ARTS-Laboratory/LPBF-Observer/system_development/Damascus/V0.5.0/software development/Event Camera/v0.2/README.md

# Python Virtual Environment Setup

## Overview

It is recommended to run the Event Camera software inside a Python virtual environment. This keeps the project's Python packages isolated from other Python installations and helps ensure that the required dependency versions are used.

> **Important:** Install the **Arena SDK** and **Arena Python API** as described below before running the Event Camera software.

------------------------------------------------------------------------

## Create a Virtual Environment

Open Command Prompt or PowerShell and navigate to the Event Camera project directory.

Create a Python virtual environment named `megaforehead`:

```bash
python -m venv megaforehead
```

Activate the virtual environment.

### Windows

```bash
megaforehead\Scripts\activate
```

### Linux

```bash
source megaforehead/bin/activate
```

Once activated, the terminal should show `(.venv)` before the command prompt.

------------------------------------------------------------------------

## Install the Project Requirements

With the virtual environment activated, install the Python packages listed in `requirements.txt`:

```bash
python -m pip install -r requirements.txt
```

> **Note:** The `arena_api` package is supplied with the LUCID Arena SDK. If installation from `requirements.txt` cannot locate `arena_api`, install the Arena Python wheel from the Arena SDK as described in the **Arena Python API Installation** section below.

------------------------------------------------------------------------

# Arena SDK Installation Guide

## Overview

The camera software requires the **LUCID Arena SDK** to be installed before the camera can be detected and used.

> **Important:** During installation, you **must** enable **Developer Mode**. Failing to do so will result in missing development components required by the application.

------------------------------------------------------------------------

## Download the Arena SDK

Download the Arena SDK installer using the link below (You must make an account with Lucid):

**Arena SDK Installer:**

[Arena SDK Installer](https://thinklucid.com/downloads-hub/)

------------------------------------------------------------------------

## Installation Instructions

1. Download the Arena SDK installer from the link above.
2. Run the installer with administrator privileges.
3. Follow the installation wizard.
4. When prompted to select installation options, **enable Developer Mode**.

------------------------------------------------------------------------

## ⚠️ Critical Requirement: Enable Developer Mode

> **Developer Mode must be selected during installation.**

If Developer Mode is **not** selected:

- Required development libraries and headers will not be installed.
- The application may fail to detect or communicate with the camera.
- Camera SDK components required by the application will be missing.
- You may encounter runtime errors or application startup failures.
- The SDK may need to be completely reinstalled to add the missing components.

**Verify that the "Developer Mode" option is checked before proceeding with the installation.**

------------------------------------------------------------------------

## Developer Mode Installation

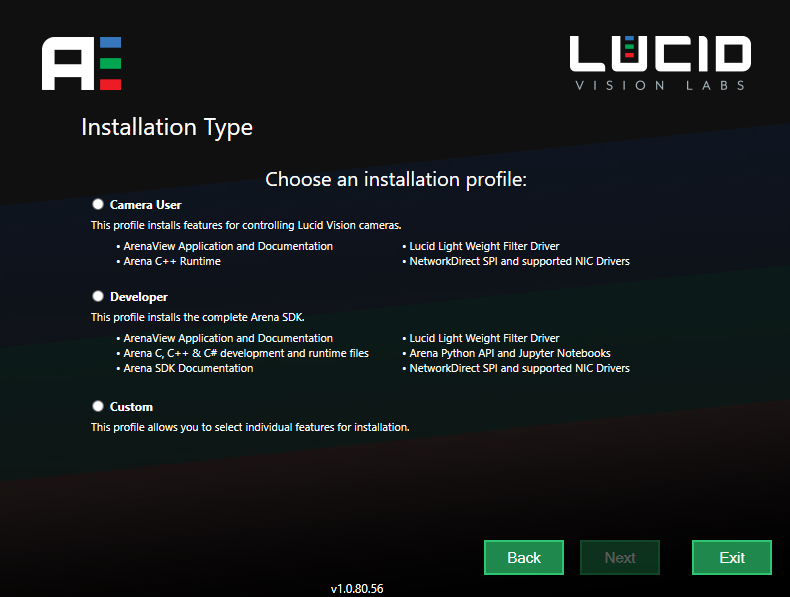
[picture p3: system_development/Damascus/V0.5.0/software development/Event Camera/v0.2/Media/DeveloperModeInstaller.png]


------------------------------------------------------------------------

## Verify the Installation

After installation:

- Launch **ArenaView**.
- Verify that your camera is detected.
- Confirm that you can start image acquisition successfully.
- If the camera is not detected, verify that Developer Mode was enabled during installation.

------------------------------------------------------------------------

## Troubleshooting

If the application cannot communicate with the camera:

1. Confirm that the Arena SDK is installed.
2. Verify that **Developer Mode** was selected during installation.
3. Restart the computer if prompted by the installer.
4. If Developer Mode was not selected, rerun the installer and modify or reinstall the SDK with Developer Mode enabled.

------------------------------------------------------------------------

## Additional Notes

Always install the version of the Arena SDK that matches the version required by this application. Using a different SDK version may result in compatibility issues.

# Network Adapter Configuration

## Overview

To help improve camera streaming performance and reduce dropped packets
or acquisition interruptions, configure your network adapter with the
highest supported values for the settings below.

> **Note:** Do **not** manually enter the values shown in example
> screenshots. Instead, configure each setting to the **maximum value
> allowed by your network adapter**.

## Configuration Steps

1.  Open **Network Connections**.
2.  Right-click the Ethernet adapter connected to the camera and select
    **Properties**.
3.  Click **Configure**.
4.  Open the **Advanced** tab.
5.  Locate the following settings:
    -   **Jumbo Packet**
    -   **Receive Buffer**
6.  Set each option to the **maximum value available** in the adapter's
    configuration.
7.  Click **OK** to save the changes.

------------------------------------------------------------------------

## Jumbo Packet

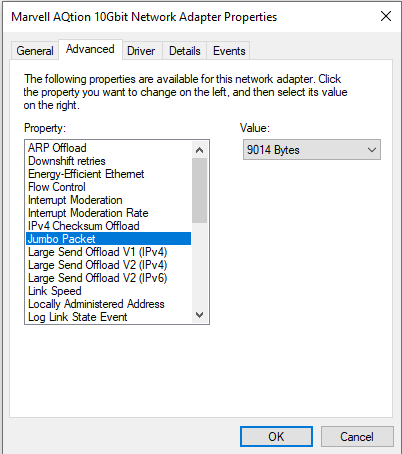
[picture p4: system_development/Damascus/V0.5.0/software development/Event Camera/v0.2/Media/JumboPacket.png]


------------------------------------------------------------------------

## Receive Buffer

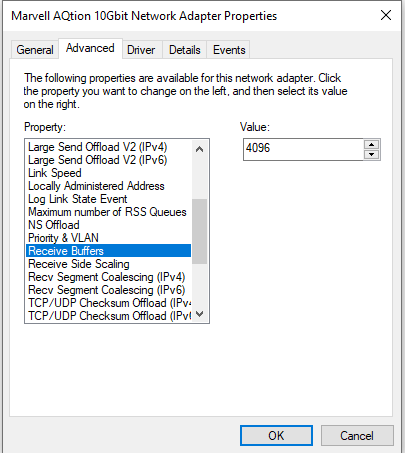
[picture p5: system_development/Damascus/V0.5.0/software development/Event Camera/v0.2/Media/ReceiveBuffers.png]


------------------------------------------------------------------------

## Notes

-   The maximum available values may differ depending on the network
    adapter manufacturer and model.
-   After changing these settings, restart the network connection or
    reboot the computer if required.
-   These settings are commonly used to improve the reliability of
    high-bandwidth GigE Vision camera streaming.

------------------------------------------------------------------------

## Verify the Device Link Speed

After configuring the network adapter, verify that the camera is operating at the expected network link speed.

### Why This Matters

If the **Device Link Speed** is lower than the camera's rated speed, the camera may experience:

- Reduced bandwidth
- Dropped packets
- Incomplete images
- Acquisition interruptions
- Reduced overall performance

### Expected Device Link Speed

The **Device Link Speed** reported in ArenaView should match the maximum speed supported by your camera.

| Camera Link Speed | Expected DeviceLinkSpeed |
|---|---:|
| 1 Gigabit (1G) | 1,000,000,000 bps |
| 2.5 Gigabit (2.5G)| 2,500,000,000 bps |
| 5 Gigabit (5G) | 5,000,000,000 bps |
| 10 Gigabit (10G)  | 10,000,000,000 bps |

### How to Check

1. Open **ArenaView**.
2. Connect to your camera.
3. Ensure the features toggle is set to "Complete" 
4. Open the **Features** panel.
5. Search for **Device Link Speed**.
6. Verify that the reported value matches your camera's expected link speed.

If the reported speed is lower than expected:

- Verify that the Ethernet adapter supports the camera's link speed.
- Confirm that the correct Ethernet port is being used.
- Check the network cable (Cat6/Cat6a recommended for higher-speed cameras).
- Ensure the network adapter drivers are up to date.
- Reboot the system after making any network configuration changes.

------------------------------------------------------------------------

## Change Packet Size Setting

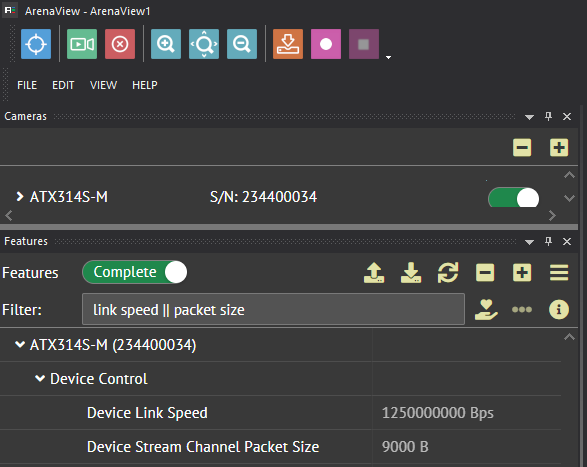
[picture p6: system_development/Damascus/V0.5.0/software development/Event Camera/v0.2/Media/9000B-Device-Stream-Channel-Packet-Size.png]


------------------------------------------------------------------------

# Arena Python API Installation

## Overview

The **Arena Python API** is a Python wrapper for the Arena SDK that allows Python applications to communicate with LUCID Vision cameras.

The Python API is built on top of the **Arena C API** and requires that the **Arena SDK** has already been installed.

> **Important:** Install the Arena SDK **before** installing the Arena Python API.

------------------------------------------------------------------------

## Prerequisites

Before installing the Arena Python API, ensure the following requirements are met:

- Python **3.6.8** or newer
- Arena SDK installed
- **pywin32** package (Windows)

Install **pywin32** using pip:

```bash
pip install pywin32
```

> **Note:** For systems without internet access, install the required dependencies using the **offline_installation_dependencies.zip** package included with the SDK.

------------------------------------------------------------------------

# Arena Python API Installation

## Overview

The **Arena Python API** is a Python wrapper for the Arena SDK that allows Python applications to communicate with LUCID Vision cameras.

The Python API is built on top of the **Arena C API** and requires that the **Arena SDK** has already been installed.

> **Important:** Install the Arena SDK **before** installing the Arena Python API.

------------------------------------------------------------------------

## Prerequisites

Before installing the Arena Python API, ensure the following requirements are met:

- Python **3.6.8** or newer
- Arena SDK installed
- **pywin32** package (Windows)

Install **pywin32** using pip:

```bash
pip install pywin32
```

> **Note:** For systems without internet access, install the required dependencies using the **offline_installation_dependencies.zip** package included with the SDK.

------------------------------------------------------------------------

## Install the Arena Python API

The Arena Python wheel (`.whl`) file is included with the Arena SDK installation.

**Default location:**

```text
C:\ProgramData\Lucid Vision Labs\ArenaView\ArenaPy
```

Before running the installation command, **pip must be able to locate the wheel file**. You can do this in one of two ways:

### Option 1 (Recommended): Navigate to the ArenaPy Directory

Open a Command Prompt or PowerShell window and change to the directory containing the wheel file:

```bash
cd "C:\ProgramData\Lucid Vision Labs\ArenaView\ArenaPy"
```

Then install the package:

```bash
pip install arena_api-<version>-py3-none-any.whl
```

------------------------------------------------------------------------

### Option 2: Install Using the Full File Path

If you are running the command from a different directory, provide the full path to the wheel file:

```bash
pip install "C:\ProgramData\Lucid Vision Labs\ArenaView\ArenaPy\arena_api-<version>-py3-none-any.whl"
```

Replace `<version>` with the version number of the wheel file included with your Arena SDK installation.

> **Important:** If the wheel file is not in your current working directory and you do not specify its full path, `pip install` will fail because it cannot locate the installation package.

------------------------------------------------------------------------

## Installing Example Dependencies

Some of the Python examples require additional Python packages.

Install them by running:

```bash
pip install -r requirements_win.txt
```

------------------------------------------------------------------------

## Running the Python Examples

The example programs are located in:

```text
C:\ProgramData\Lucid Vision Labs\Examples\src\Python Source Code Examples
```

Navigate to the examples directory:

```bash
cd "C:\ProgramData\Lucid Vision Labs\Examples\src\Python Source Code Examples"
```

Run an example using Python:

```bash
python <example_name>.py
```

For example:

```bash
python save_image.py
```

------------------------------------------------------------------------

## Verification

After installation, verify that:

- The `arena_api` package imports successfully.
- The camera is detected.
- One of the provided Python examples runs without errors.

For example:

```python
from arena_api.system import system

devices = system.create_device()
print(f"Found {len(devices)} device(s)")
```

If no errors are reported and the connected camera is detected, the installation was successful.

------------------------------------------------------------------------

## Notes

- The Arena Python API is included with the Windows installation of the Arena SDK.
- Linux users must download the Python package separately from the **LUCID Downloads Hub** and follow the instructions included with the download package.
- Ensure that the version of the Arena Python API matches the installed version of the Arena SDK.
- If multiple versions of Python are installed, verify that `pip` corresponds to the Python interpreter you intend to use (for example, `python -m pip install ...`).

------------------------------------------------------------------------
