ARTS-Laboratory/LPBF-Observer/system_development/Damascus/V0.5.1/software development/thermal_optical/iteration_2/code/npz Processor/Images/thermalRun1_20260924_181015/image_index.csv

actual_time_s
000000000
000000000
000000001
000000002
000000004
000000004
000000006
000000006
000000007
000000008
000000009
000000010
000000011
000000012
000000013
000000014
000000015
000000016
000000017
000000018
000000019
000000020
000000021
000000022
000000023
000000024
000000025
000000026
000000027
000000028
000000029
