ARTS-Laboratory/LPBF-Observer/system_development/Damascus/V0.5.1/software development/thermal_optical/iteration_2/code/npz Processor/Images/thermalRun2_20260924_190804/image_index.csv

actual_time_s
000000000
000000001
000000001
000000003
000000004
000000005
000000005
000000007
000000007
000000009
000000009
000000011
