ARTS-Laboratory/LPBF-Observer/system_development/Damascus/V0.5.1/software development/event_optical/iteration_2/Event Camera Test Parameters.xlsx

Sheet: Sheet2
 | LASER |  |  |  |  | EVENT CAMERA
test | Defocus | speed (mm/s) | power (W) | Weld Successful? | what failed? | Pos. Event Bias | Neg. Event Bias | Lowpass cutoff | Refractory period | Filter(s) | Date | Run | Notes | Comment
1 | 5.873 | 45 | 300 | Yes |  | 0 | 0 |  |  |  |  |  | 150 micron defocus
2 | 5.873 | 60 | 300 | Yes |  | 5 | 5
3 | 5.873 | 75 | 300 | Yes |  | 5 | 5
4 | 5.873 | 90 | 300 | Yes |  | 10 | 10
5 | 5.873 | 105 | 300 | No |  | 15 | 15
6 | 5.873 | 120 | 300 | No |  | 2 | 2
7 | 5.873 | 135 | 300 | No |  | 0 | 0
8 | 5.873 | 150 | 300 | No |  | 5 | 5
9 | 5.873 | 165 | 300 | Yes |  | 5 | 5
10 | 5.873 | 180 | 300 | No |  | 5 | 5 | 20 | -20
11 | 5.873 | 75 | 300 |  |  | 0 | 0 |  |  | UV | 2026-08-28
12 | 5.873 | 75 | 300 |  |  | 0 | 0 |  |  | UV | 2026-08-28
13 | 5.873 | 75 | 300 |  |  | 1 | 1 | None | None | UV | 2026-08-28 |  | No low pass cut off and refractory
14 | 5.873 | 75 | 300 |  |  | 5 | 5 | None | None | UV | 2026-08-28
15 | 5.873 | 75 | 300 |  |  | 3 | 3 |  |  |  | 2026-08-28
16 | 5.873 | 75 | 300 |  |  | 2 | 2 |  |  |  | 2026-08-28
17 | 5.873 | 75 | 300 |  |  | 0 | 0 |  |  | Red 635 | 2026-08-28
18 | 5.873 | 75 | 300 |  |  | 0 | 0 |  |  | Red 635 + UV | 2026-08-28 |  |  | looks good! spatter clearly seen
19 | 5.873 | 75 | 300 |  |  | 0 | 0 |  |  | polycarb (PC) | 2026-08-31
20 | 5.873 | 75 | 300 |  |  | 0 | 0 |  |  | PC + Red | 2026-08-31
21 | 5.873 | 75 | 300 |  |  | 0 | 0 |  |  | PC + Red + UV | 2026-08-31 |  |  | only saw negative (blue) events
22 | 5.873 | 75 | 300 |  |  | 0 | 0 |  |  | PC + Red | 2026-09-04 | 0 | no buffer (oldest first), record for longer (upto 600k events) | very noisey, whole block becomes red
23 | 5.873 | 75 | 300 |  |  | 0 | 0 |  |  | PC + Red | 2026-09-04 | 1 | started laser @ 100k events | minimal noise, clear circle shape seen
24 | 5.873 | 75 | 300 |  |  | 0 | 0 |  |  | PC + Red | 2026-09-04 | 2 | started laser @ 80k events | concentric blobs
25 | 5.873 | 75 | 300 |  |  | 0 | 0 |  |  | PC + Red | 2026-09-04 | 3 | started laser @ 50k | spatter looks like a flame
26 | 5.873 | 75 | 300 |  |  | 0 | 0 |  |  | PC + Red | 2026-09-04 | 4 | started @ 100k, consistent regen speeds | nothing…
27 | 5.873 | 75 | 300 |  |  | 0 | 0 |  |  | PC + Red | 2026-09-04 | 5 | idk looks good | small red, big blue
28 | 5.873 | 75 | 300 |  |  | 0 | 0 |  |  | PC + Red | 2026-09-04 | 6 | consistent process | red -> blue -> red again?
29 | 5.873 | 75 | 300 |  |  | 0 | 0 |  |  | PC + Red + UV | 2026-09-04 | 7 | start @100k, low activity | nothing…
30 |  |  |  |  |  |  |  |  |  | PC + Red + UV | 2026-09-04 | 8 | max activity = 300k | laser path heat trail visible (?) in first few frames, then risidual heat areas
31 |  |  |  |  |  |  |  |  |  | PC + Red + UV | 2026-09-04 | 9 | weird, prev test was anomolus | nothing…
32 |  |  |  |  |  |  |  |  |  | PC | 2026-09-04 | 10 | nothing when start @ 100k | nothing…
33 |  |  |  |  |  |  |  |  |  | PC | 2026-09-04 | 11 | somehting when start @ 150k | blobby blue and red
34 |  |  |  |  |  |  |  |  |  | PC | 2026-09-04 | 12 | sanity check prev, -> 600k! | realization: spatter appears after the weld (spatter radiates from end point)
35 |  |  |  |  |  |  |  |  |  | PC + UV | 2026-09-04 | 13 | starting @ 150k moving forward | bright, radial spatter, vertical spatter
36 |  |  |  |  |  |  |  |  |  | PC + UV | 2026-09-04 | 14 |  | very blobby
37 |  |  |  |  |  |  |  |  |  | PC + yellow 610 | 2026-09-04 | 15 |  | firework spatter, circle path distinguishabel
38 |  |  |  |  |  |  |  |  |  | PC + yellow 610 | 2026-09-04 | 16 | up to 1E6 events!
39
40
41
 | Dr Yuan said 400 micron defocus (13.179) should work for a bigger spot size, and 300W is low, 800W is realistic. Also careful about the spatter coming up into the tool head at high powers, need to use glass or at least gas flow to protect laser optics

Sheet: Sheet1
test | Defocus (150 microns) | speed (mm/s) | power (W) | Weld Successful? (Left, Right) |  | Nickel Strip Fail? (Left, Right) |  | Weld Fail? (Left, Right)
1 | 5.873 | 45 | 200 | Yes | No | Yes | N/A | No | weld fail
2 | 5.873 | 45 | 200 | No | Yes | N/A | Yes | weld fail? (Left, Right) | No
3 | 5.873 | 45 | 225 | Yes | No | Yes | N/A | No | weld fail
4 | 5.873 | 45 | 225 | Yes | Yes | No | Yes | Yes | No
5 | 5.873 | 45 | 250 | Yes | Yes | Yes | Yes | No | No
6 | 5.873 | 45 | 250 | No | Yes | N/A | Yes | weld fail | No
7.1 | 5.873 | 45 | 275 | No | No | N/A | N/A | weld fail | weld fail
7.2 | 5.873 | 45 | 275 | Yes | No | Yes | N/A | No | weld fail
8 | 5.873 | 45 | 275 | Yes | No | Yes | N/A | No | weld fail
9 | 5.873 | 45 | 300 | Yes | yes | Yes | N/A | No | weld fail
10 | 5.873 | 45 | 300 | Yes | Yes | Yes | Yes | No | No
Date | 3_13_2026
 |  |  |  | Weld Successful? | what failed?
Test | 5.873 | 45 | 300 | Yes | Nickel Strip
1 | 5.873 | 45 | 300 | Yes | Nickel Strip
2 | 5.873 | 45 | 300 | Yes | Nickel Strip
3 | 5.873 | 60 | 300 | No | Weld Failed During Printing
4 | 5.873 | 60 | 300 | Yes | Nickel Strip
5 | 5.873 | 75 | 300 | Yes | Nickel Strip
6 | 5.873 | 75 | 300 | No | Weld Fail
7 | 5.873 | 90 | 300 | Yes | Nickel Strip
8 | 5.873 | 90 | 300 | Yes | Nickel Strip
9 | 5.873 | 105 | 300 | No | Weld Failed During Printing
10 | 5.873 | 105 | 300 | Yes | Both
1 | Yes
2 | Yes
3 | No
4 | Yes
5 | Yes
6 | No
7 | Yes
8 | Yes
9 | No
10 | Yes
