ARTS-Laboratory/LPBF-Observer/general_use/Head Plate Parts/STEP/Head Plate Insert.stp

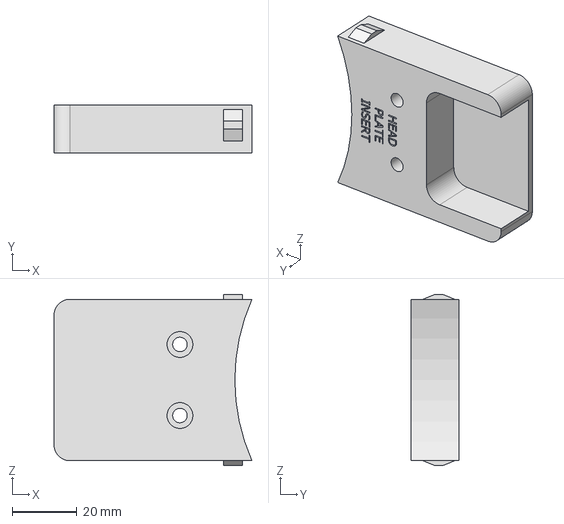
[picture p22: CAD file, 2026-04-30]
general_use/Head Plate Parts/STEP/Head Plate Insert.stp
61.3 x 15.0 x 53.0 mm
