ARTS-Laboratory/LPBF-Observer/general_use/Reference Prints/Associated models/Rounded Square.stp

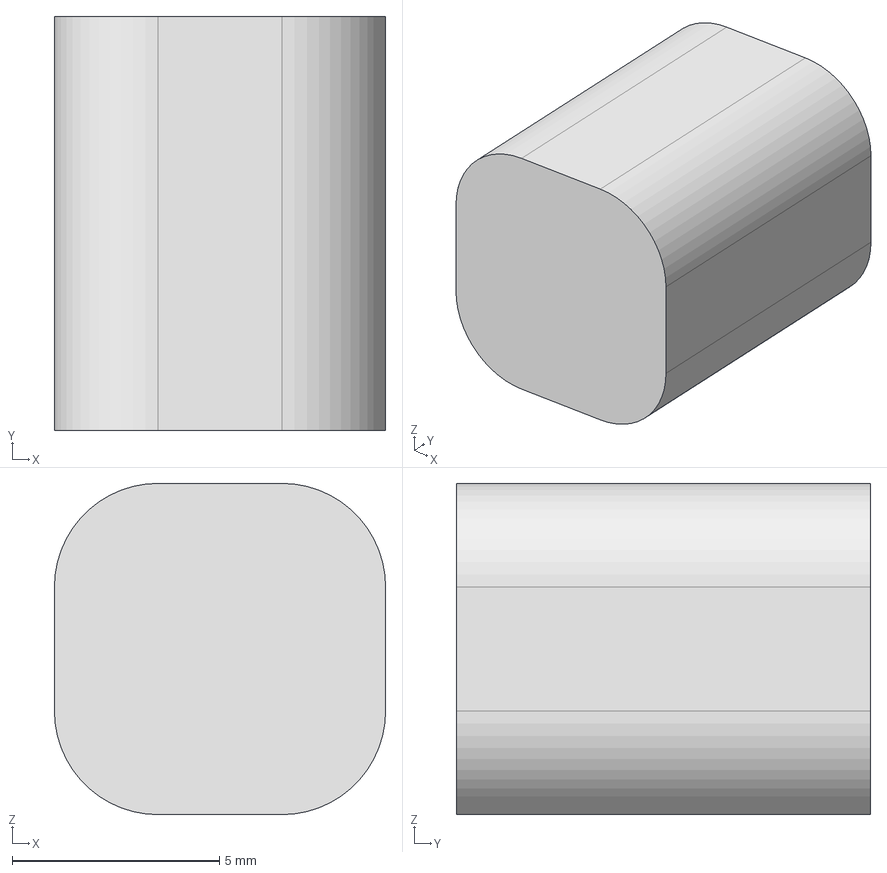
[picture p23: CAD file, 2026-07-31]
general_use/Reference Prints/Associated models/Rounded Square.stp
8.00 x 10.0 x 8.00 mm
