ARTS-Laboratory/LPBF-Observer/general_use/Reference Prints/Flower.stl

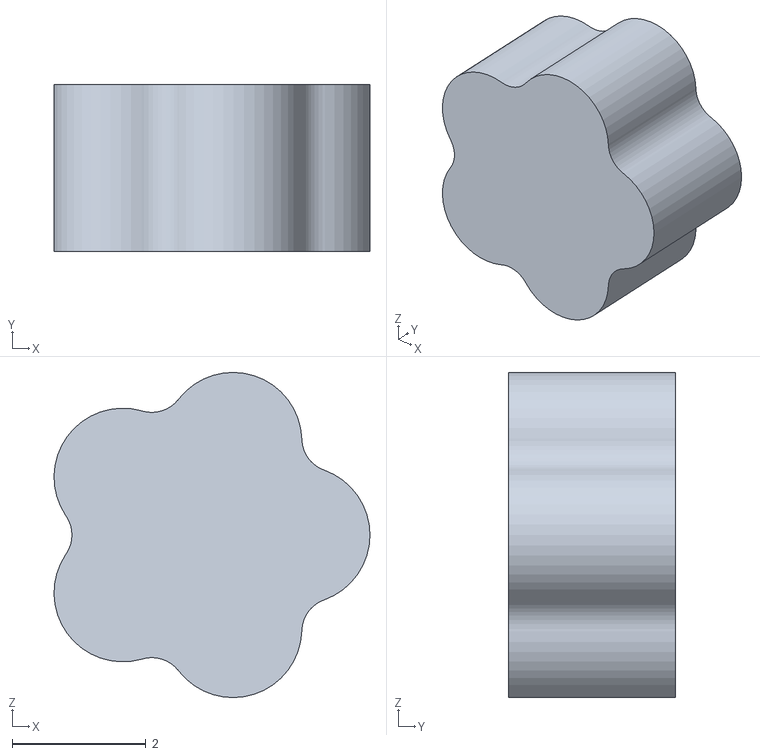
[picture p24: CAD file, 2026-04-30]
general_use/Reference Prints/Flower.stl
4.72 x 2.50 x 4.86
