ARTS-Laboratory/LPBF-Observer/system_development/Birmingham/v0.4/hardware_design/STEP Files/Optical Lid.stp

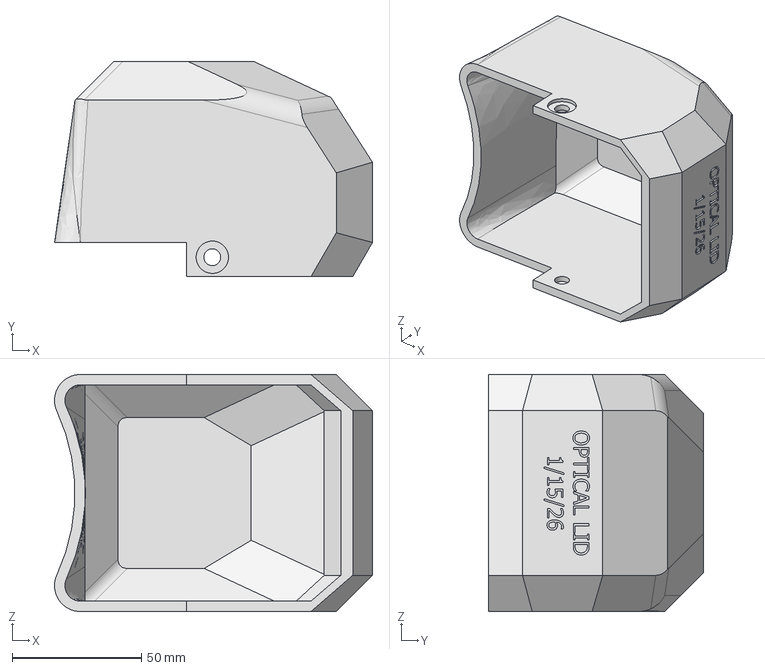
[picture p25: CAD file, 2026-04-30]
system_development/Birmingham/v0.4/hardware_design/STEP Files/Optical Lid.stp
122.9 x 83.2 x 91.6 mm
