ARTS-Laboratory/LPBF-Observer/system_development/Damascus/V0.5.1/hardware development/Step Files/Damascus Center Cylinder.stp

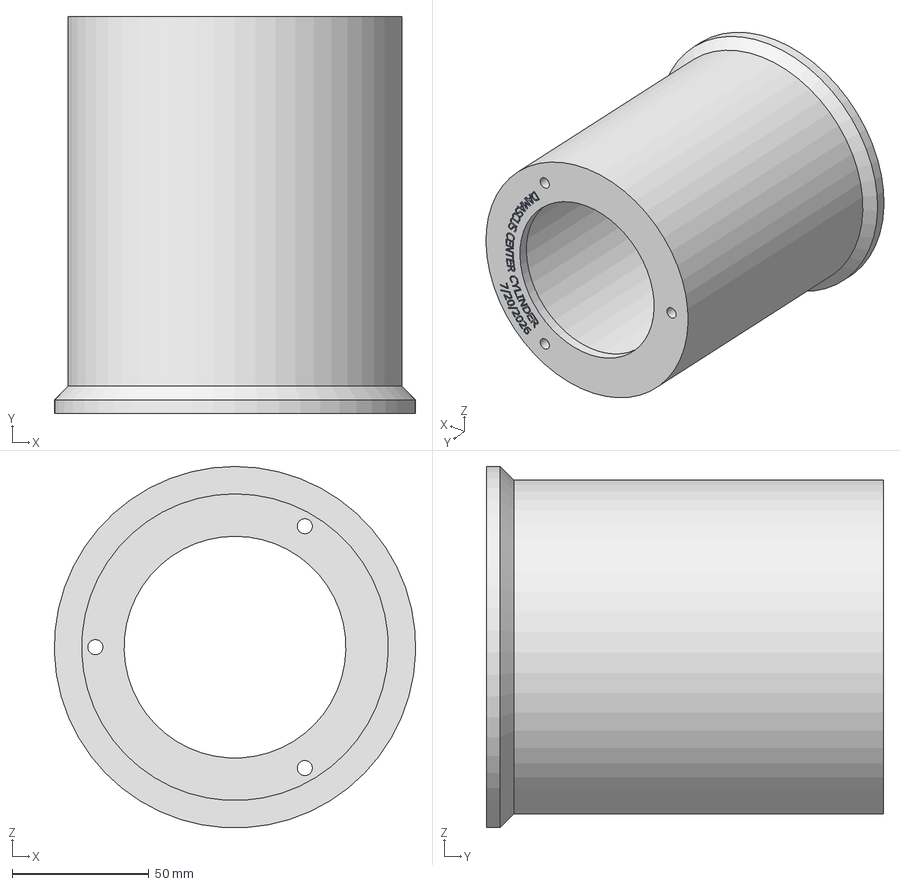
[picture p26: CAD file, 2026-07-20]
system_development/Damascus/V0.5.1/hardware development/Step Files/Damascus Center Cylinder.stp
131.9 x 145.0 x 131.9 mm
