ARTS-Laboratory/LPBF-Observer/system_development/Pittsburgh/v0.2/hardware_development/STEP Files/Thermal Camera v0.2.stp

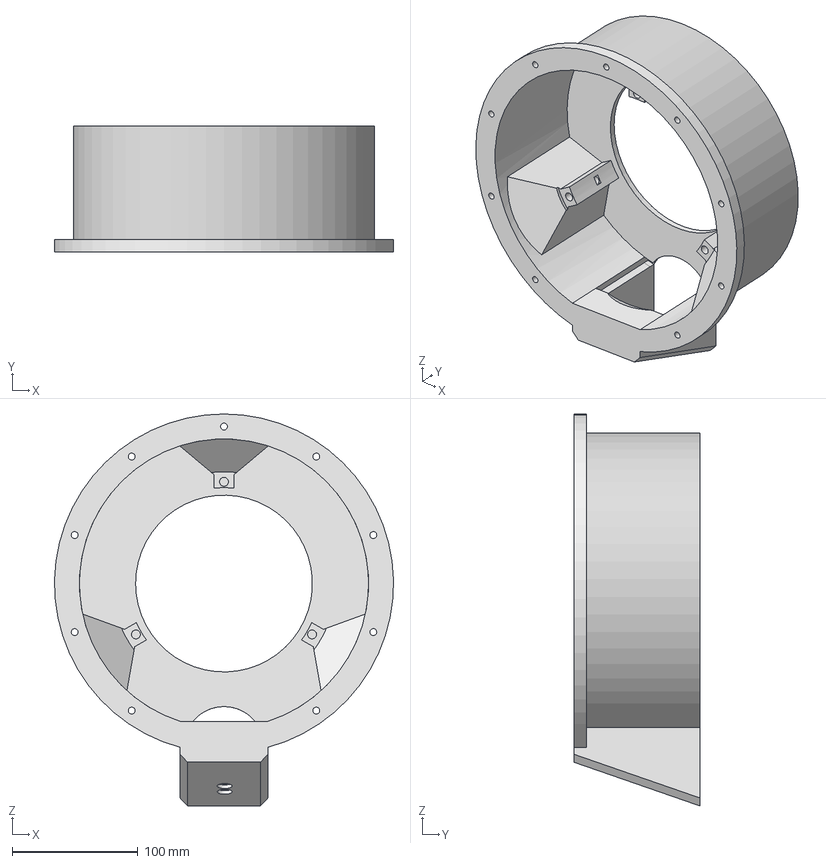
[picture p27: CAD file, 2026-04-30]
system_development/Pittsburgh/v0.2/hardware_development/STEP Files/Thermal Camera v0.2.stp
269.9 x 100.5 x 312.1 mm
