ARTS-Laboratory/LPBF-Observer/general_use/Battery Holder/STEP files/Battery Holder (Bottom) 1 Cell.stp

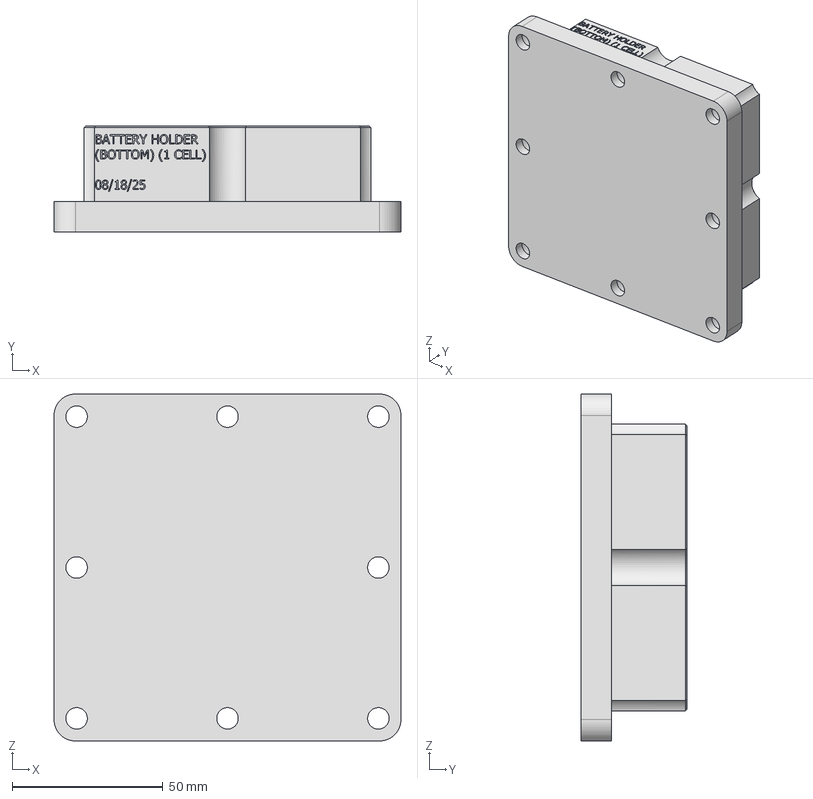
[picture p28: CAD file, 2026-04-30]
general_use/Battery Holder/STEP files/Battery Holder (Bottom) 1 Cell.stp
115.0 x 35.0 x 115.0 mm
