ARTS-Laboratory/LPBF-Observer/general_use/Reference Prints/shape-star-5-points.stl

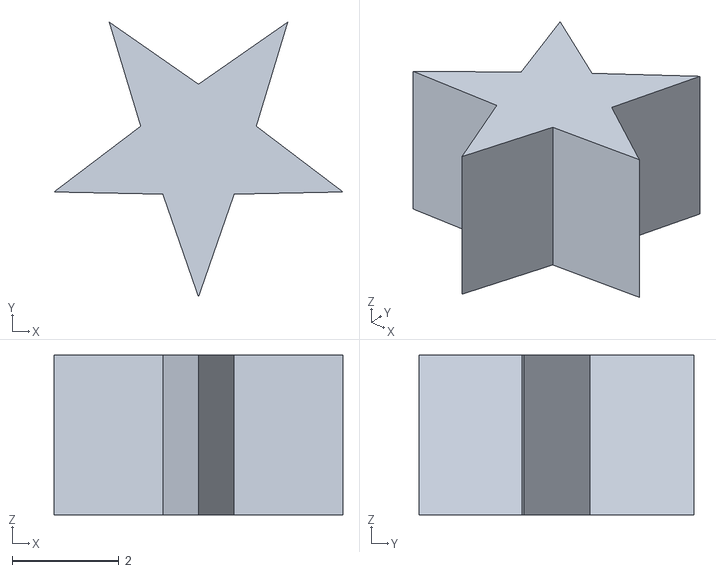
[picture p29: CAD file, 2026-04-30]
general_use/Reference Prints/shape-star-5-points.stl
5.42 x 5.16 x 3.00
