ARTS-Laboratory/LPBF-Observer/system_development/Birmingham/v0.4/hardware_design/STEP Files/Camera Cylinder Housing - Red Lights.stp

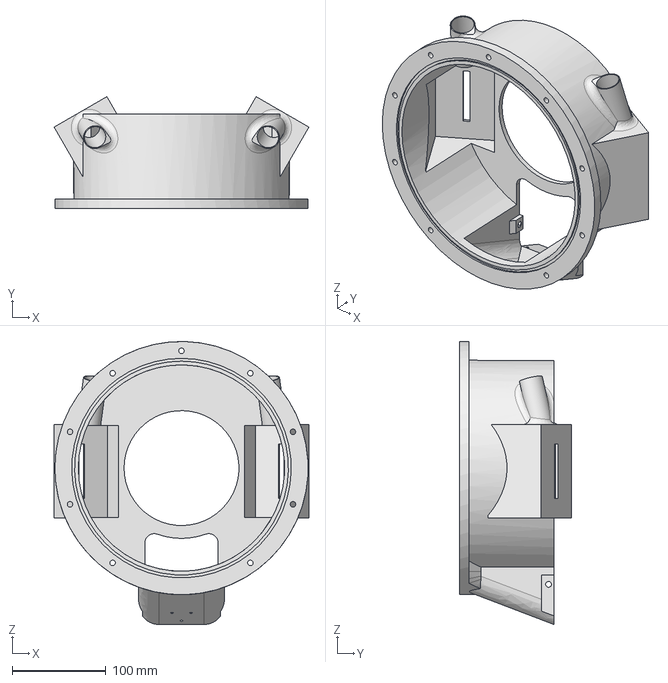
[picture p30: CAD file, 2026-04-30]
system_development/Birmingham/v0.4/hardware_design/STEP Files/Camera Cylinder Housing - Red Lights.stp
271.7 x 119.1 x 301.8 mm
