ARTS-Laboratory/LPBF-Observer/system_development/Damascus/V0.5.1/hardware development/Step Files/Dual Camera Base v2.stp

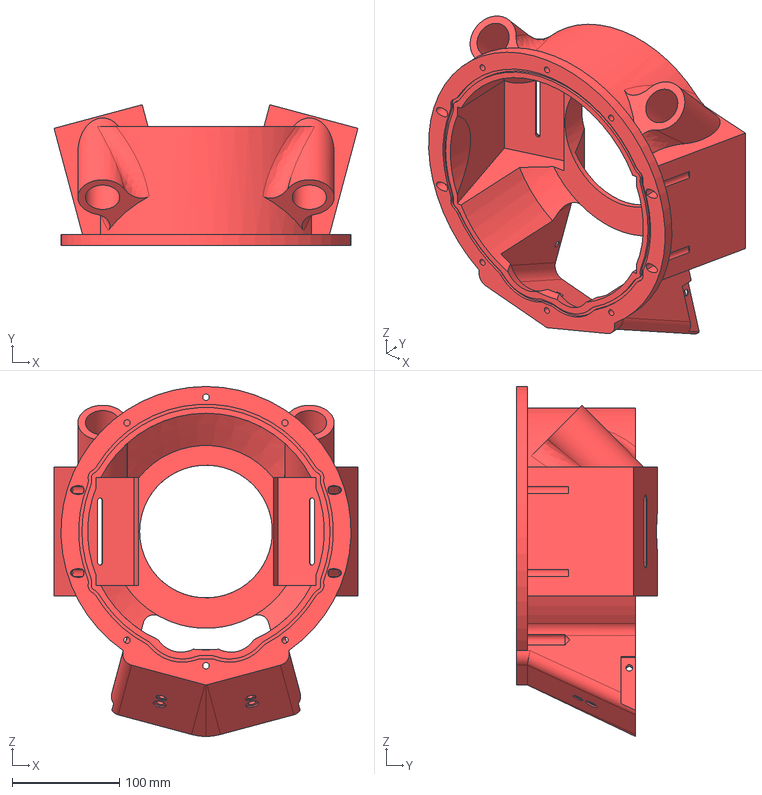
[picture p31: CAD file, 2026-07-02]
system_development/Damascus/V0.5.1/hardware development/Step Files/Dual Camera Base v2.stp
283.0 x 130.9 x 325.8 mm
