ARTS-Laboratory/LPBF-Observer/system_development/Pittsburgh/v0.2/hardware_development/STEP Files/New Thermal Housing.stp

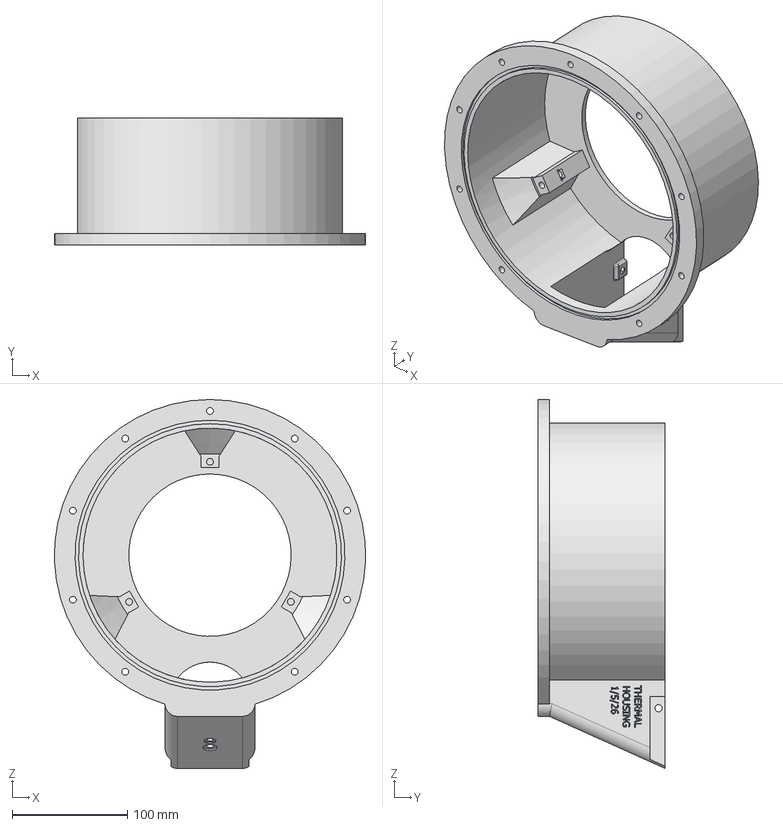
[picture p32: CAD file, 2026-04-30]
system_development/Pittsburgh/v0.2/hardware_development/STEP Files/New Thermal Housing.stp
269.8 x 110.5 x 320.0 mm
