ARTS-Laboratory/LPBF-Observer/general_use/Battery Holder/STEP files/Battery Holder (Top) 18 Cells.stp

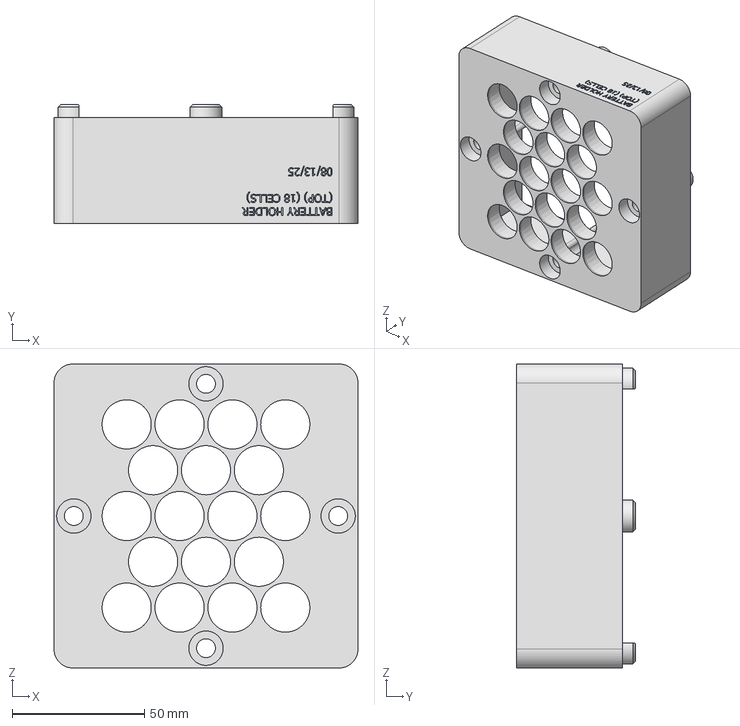
[picture p33: CAD file, 2026-04-30]
general_use/Battery Holder/STEP files/Battery Holder (Top) 18 Cells.stp
115.0 x 45.0 x 115.0 mm
