ARTS-Laboratory/LPBF-Observer/general_use/Reference Prints/shape-polygon-6-sides.stl

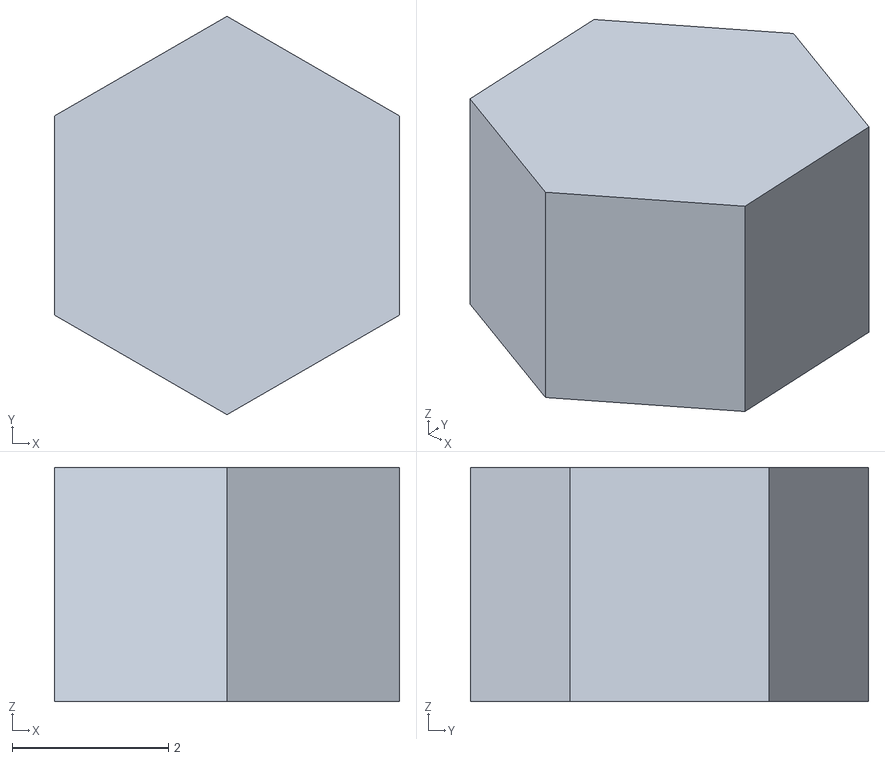
[picture p34: CAD file, 2026-04-30]
general_use/Reference Prints/shape-polygon-6-sides.stl
4.42 x 5.10 x 3.00
