ARTS-Laboratory/LPBF-Observer/system_development/Damascus/V0.5.1/hardware development/Step Files/randomCrap.3mf

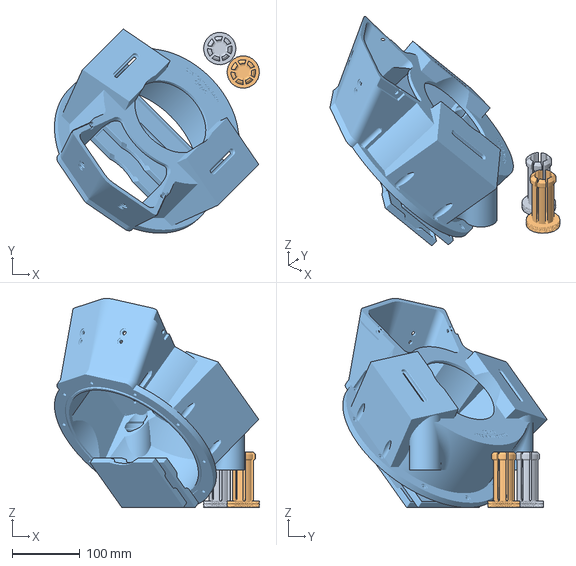
[picture p36: CAD file, 2026-07-02]
system_development/Damascus/V0.5.1/hardware development/Step Files/randomCrap.3mf
302.4 x 301.4 x 308.5 mm
WirePlugs.stp x 2
Assembly
