ARTS-Laboratory/LPBF-Observer/general_use/Battery Holder/STEP files/Shield.stp

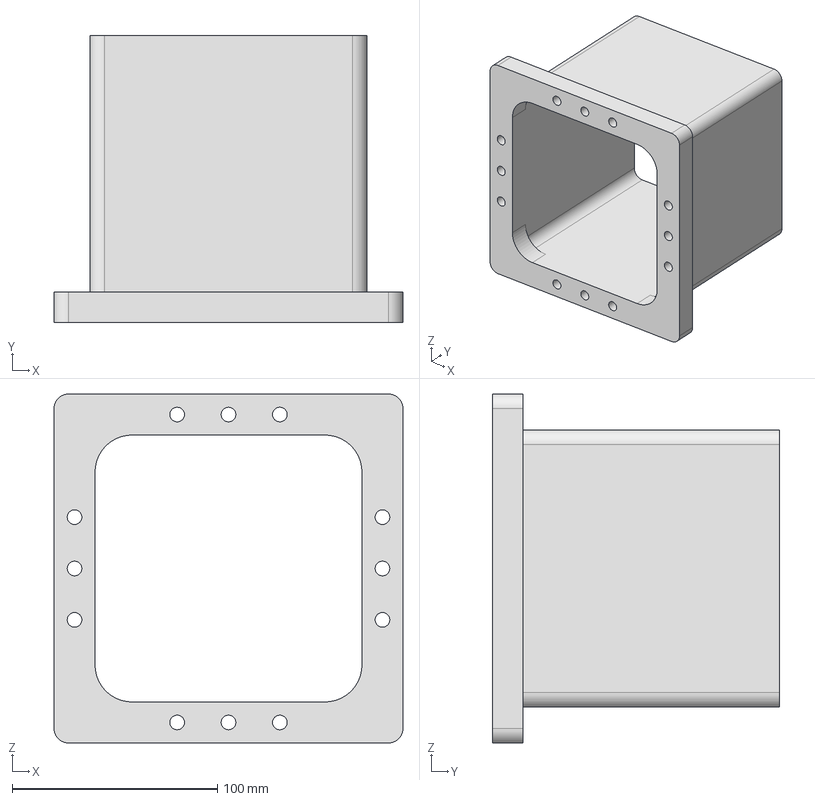
[picture p37: CAD file, 2026-04-30]
general_use/Battery Holder/STEP files/Shield.stp
170.0 x 140.0 x 170.0 mm
