ARTS-Laboratory/LPBF-Observer/general_use/Reference Prints/shape-flower.stl

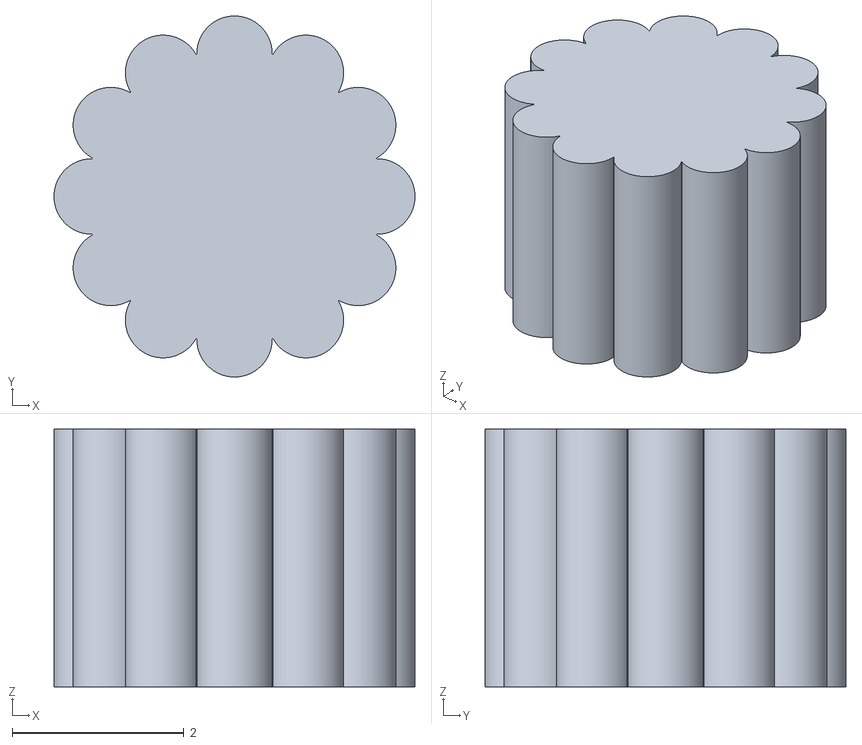
[picture p38: CAD file, 2026-04-30]
general_use/Reference Prints/shape-flower.stl
4.20 x 4.20 x 3.00
