ARTS-Laboratory/LPBF-Observer/system_development/Birmingham/v0.4/hardware_design/STEP Files/Optical Housing 2_27_26.stp

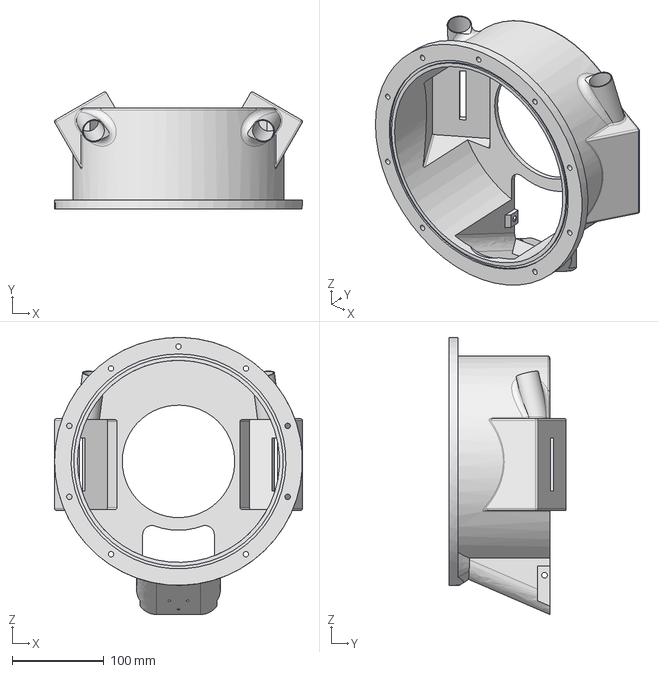
[picture p39: CAD file, 2026-04-30]
system_development/Birmingham/v0.4/hardware_design/STEP Files/Optical Housing 2_27_26.stp
270.2 x 127.9 x 301.7 mm
