ARTS-Laboratory/LPBF-Observer/system_development/Damascus/V0.5.1/hardware development/Step Files/WirePlugs.stp

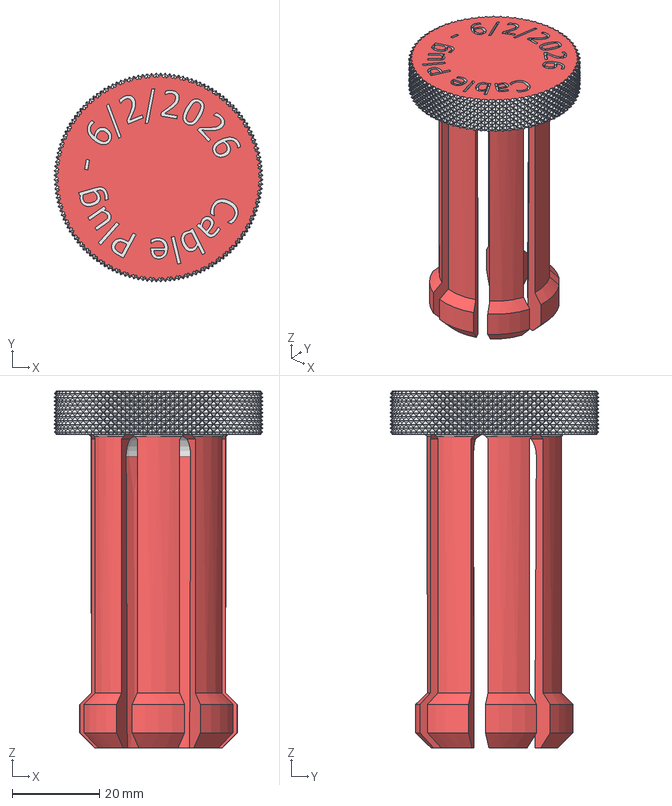
[picture p40: CAD file, 2026-07-02]
system_development/Damascus/V0.5.1/hardware development/Step Files/WirePlugs.stp
48.0 x 48.0 x 82.0 mm
