ARTS-Laboratory/LPBF-Observer/system_development/Pittsburgh/v0.2/hardware_development/STEP Files/Thermal Cover Lid.stp

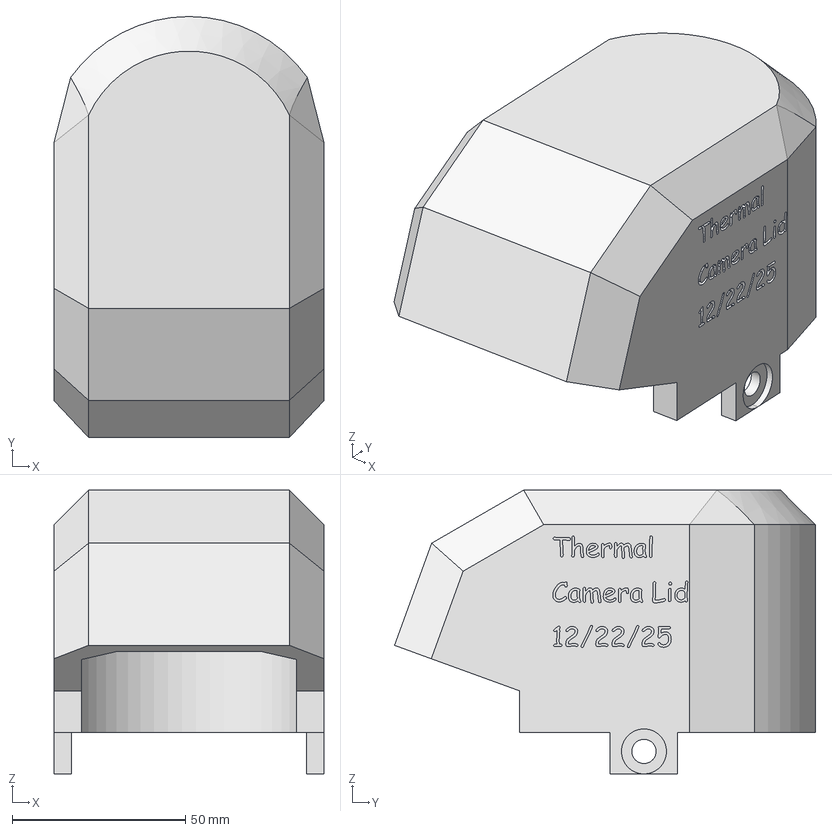
[picture p41: CAD file, 2026-04-30]
system_development/Pittsburgh/v0.2/hardware_development/STEP Files/Thermal Cover Lid.stp
78.0 x 121.6 x 82.0 mm
