ARTS-Laboratory/LPBF-Observer/general_use/Battery Holder/STEP files/Battery Holder (Top).stp

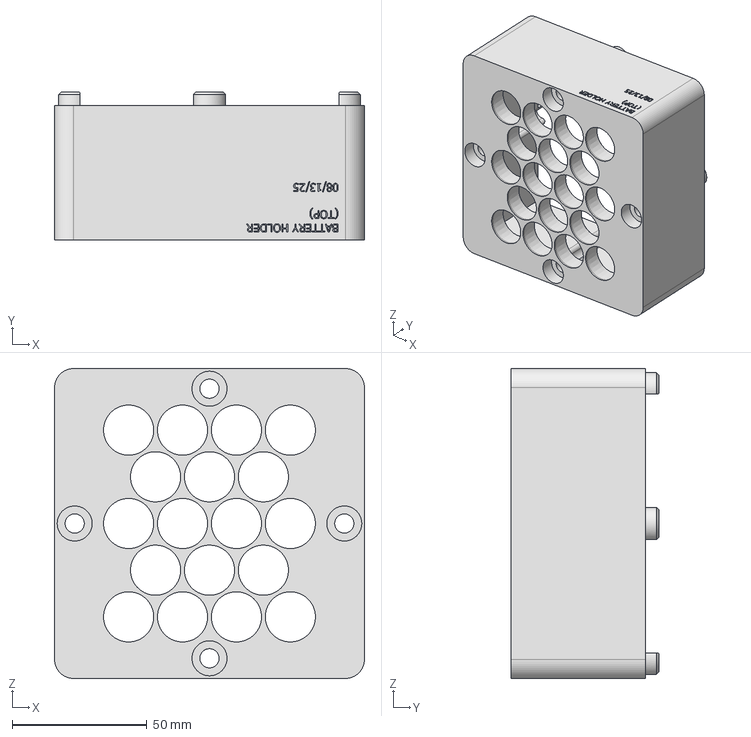
[picture p42: CAD file, 2026-04-30]
general_use/Battery Holder/STEP files/Battery Holder (Top).stp
115.0 x 55.0 x 115.0 mm
