ARTS-Laboratory/LPBF-Observer/general_use/Reference Prints/shape-circle.stl

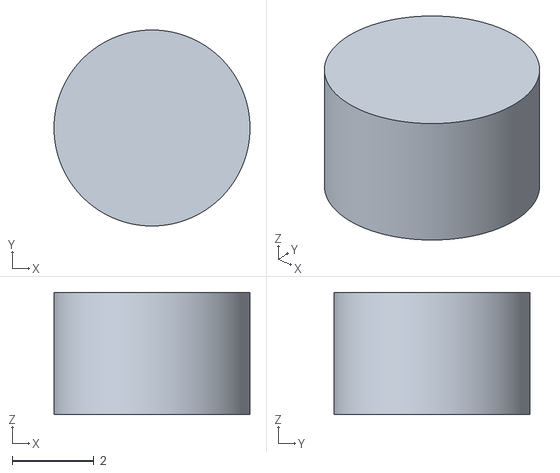
[picture p43: CAD file, 2026-04-30]
general_use/Reference Prints/shape-circle.stl
4.80 x 4.80 x 3.00
