ARTS-Laboratory/LPBF-Observer/system_development/Birmingham/v0.4/hardware_design/STEP Files/SealedGlassRing12-16-25.stp

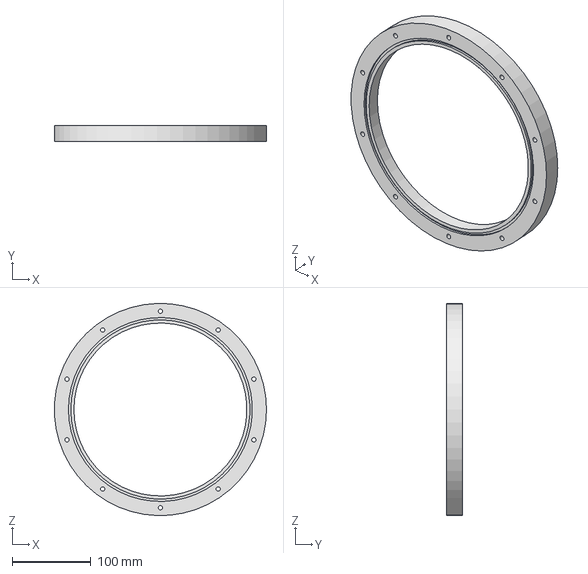
[picture p44: CAD file, 2026-04-30]
system_development/Birmingham/v0.4/hardware_design/STEP Files/SealedGlassRing12-16-25.stp
269.7 x 20.0 x 269.9 mm
