ARTS-Laboratory/LPBF-Observer/general_use/Battery Holder/STEP files/CLAMP.stp

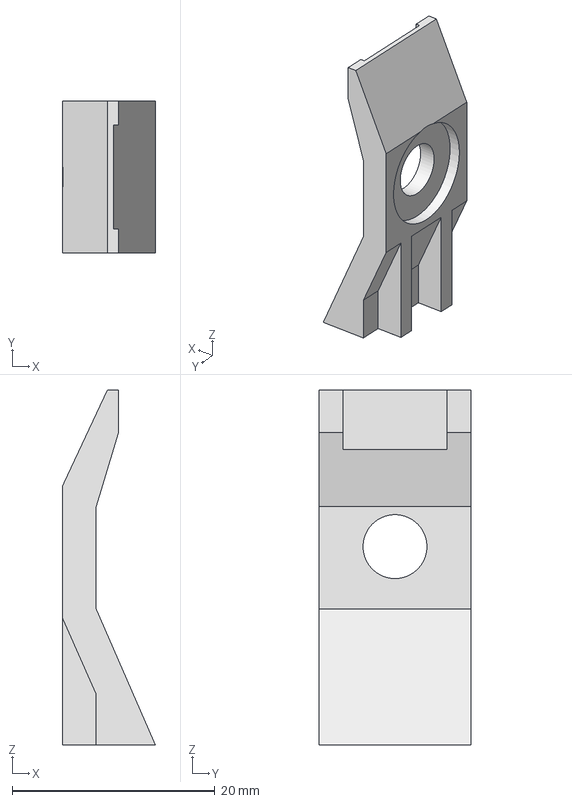
[picture p45: CAD file, 2026-03-24]
general_use/Battery Holder/STEP files/CLAMP.stp
9.15 x 15.0 x 35.0 mm
