ARTS-Laboratory/LPBF-Observer/system_development/Birmingham/v0.4/hardware_design/STEP Files/Optical Housing.stp

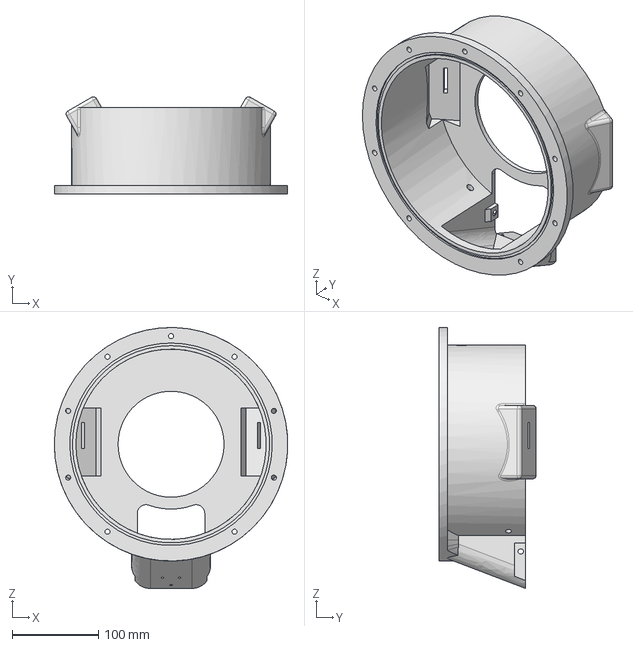
[picture p46: CAD file, 2026-04-30]
system_development/Birmingham/v0.4/hardware_design/STEP Files/Optical Housing.stp
269.9 x 112.6 x 301.8 mm
