ARTS-Laboratory/LPBF-Observer/system_development/Pittsburgh/v0.2/hardware_development/STEP Files/lid.3mf

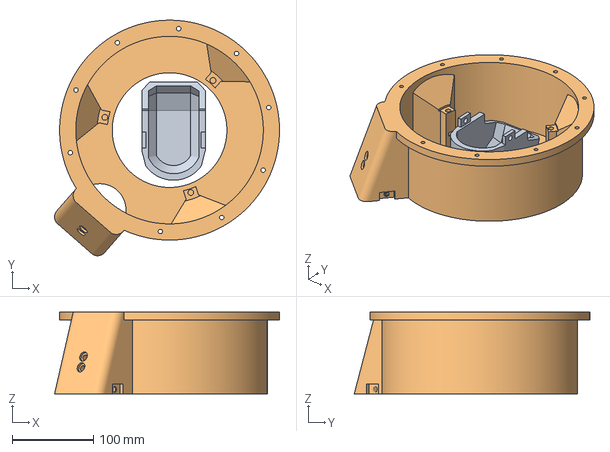
[picture p47: CAD file, 2026-04-30]
system_development/Pittsburgh/v0.2/hardware_development/STEP Files/lid.3mf
276.3 x 289.4 x 100.5 mm
lid.stp
Cylinder Slidey Bit Housing Camera Last.stp
