ARTS-Laboratory/LPBF-Observer/system_development/Birmingham/v0.4/hardware_design/STEP Files/Light Box Testing.stp

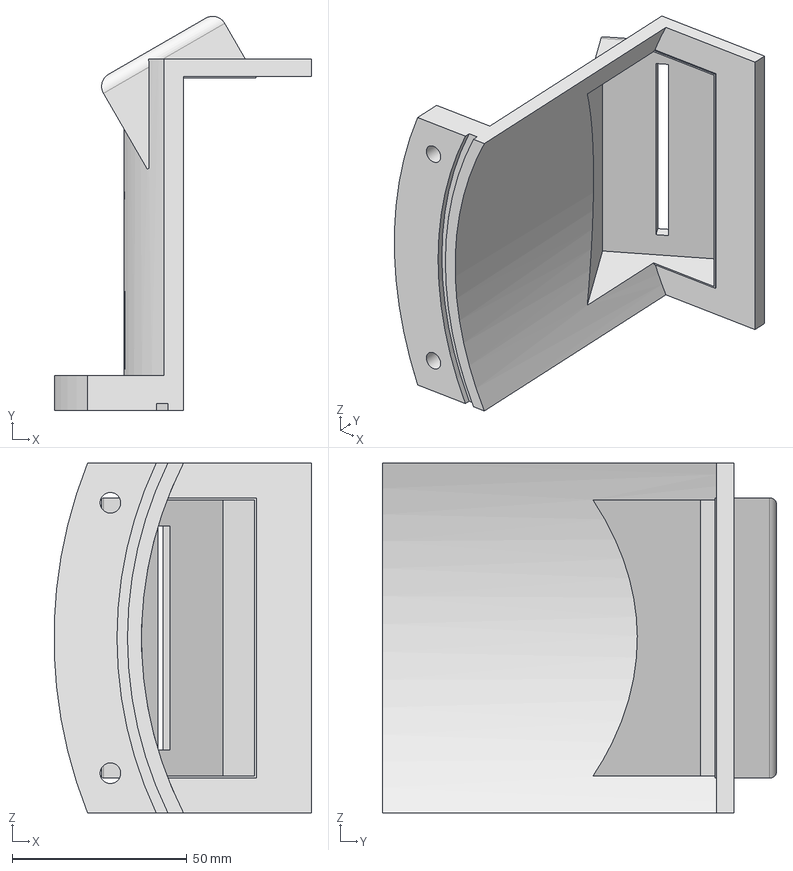
[picture p48: CAD file, 2026-04-30]
system_development/Birmingham/v0.4/hardware_design/STEP Files/Light Box Testing.stp
73.6 x 112.6 x 100.0 mm
