ARTS-Laboratory/LPBF-Observer/system_development/Damascus/V0.5.1/hardware development/Step Files/adapter-optical.stp

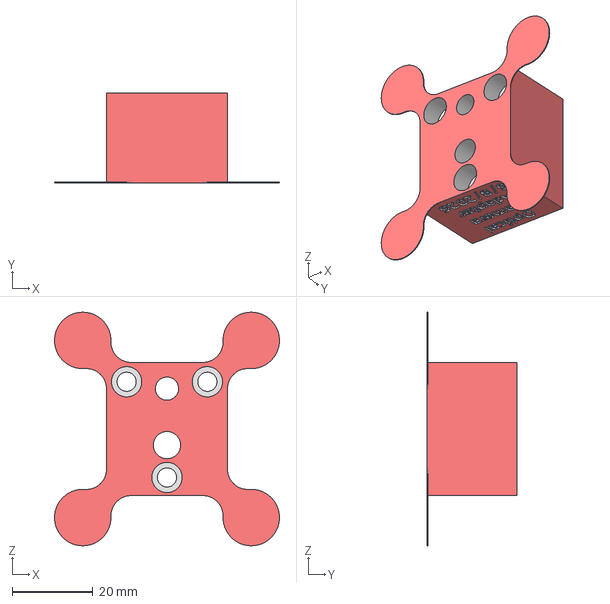
[picture p49: CAD file, 2026-06-11]
system_development/Damascus/V0.5.1/hardware development/Step Files/adapter-optical.stp
55.7 x 22.2 x 57.9 mm
