ARTS-Laboratory/LPBF-Observer/system_development/Pittsburgh/v0.2/hardware_development/STEP Files/Plastic Clamp Arm.stp

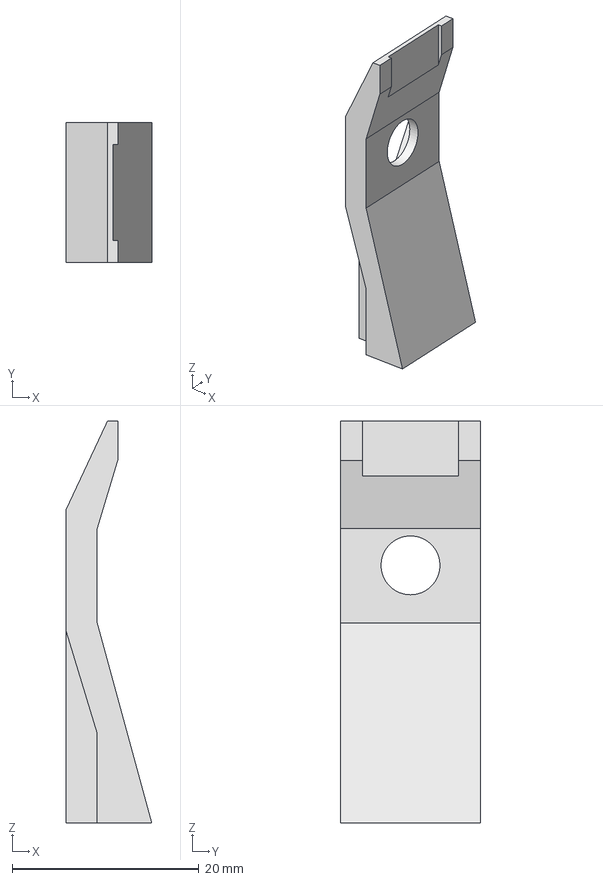
[picture p50: CAD file, 2026-04-30]
system_development/Pittsburgh/v0.2/hardware_development/STEP Files/Plastic Clamp Arm.stp
9.15 x 15.0 x 43.0 mm
