ARTS-Laboratory/LPBF-Observer/system_development/Birmingham/v0.4/hardware_design/STEP Files/Mithril Center Cylinder.stp

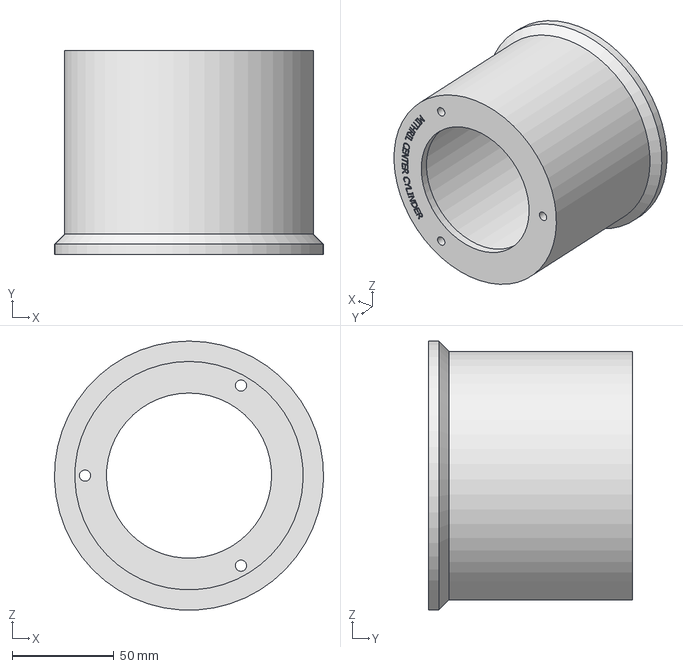
[picture p51: CAD file, 2026-04-30]
system_development/Birmingham/v0.4/hardware_design/STEP Files/Mithril Center Cylinder.stp
131.9 x 100.0 x 131.9 mm
