ARTS-Laboratory/LPBF-Observer/system_development/Birmingham/v0.4/hardware_design/STEP Files/Adapter.stp

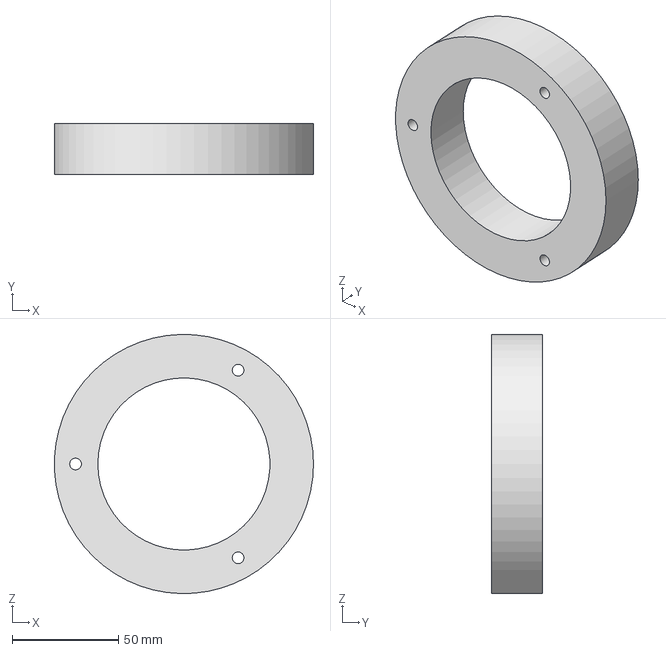
[picture p52: CAD file, 2026-03-24]
system_development/Birmingham/v0.4/hardware_design/STEP Files/Adapter.stp
121.9 x 24.0 x 122.0 mm
