ARTS-Laboratory/LPBF-Observer/system_development/Damascus/V0.5.1/hardware development/Step Files/Dual Camera Lid.stp

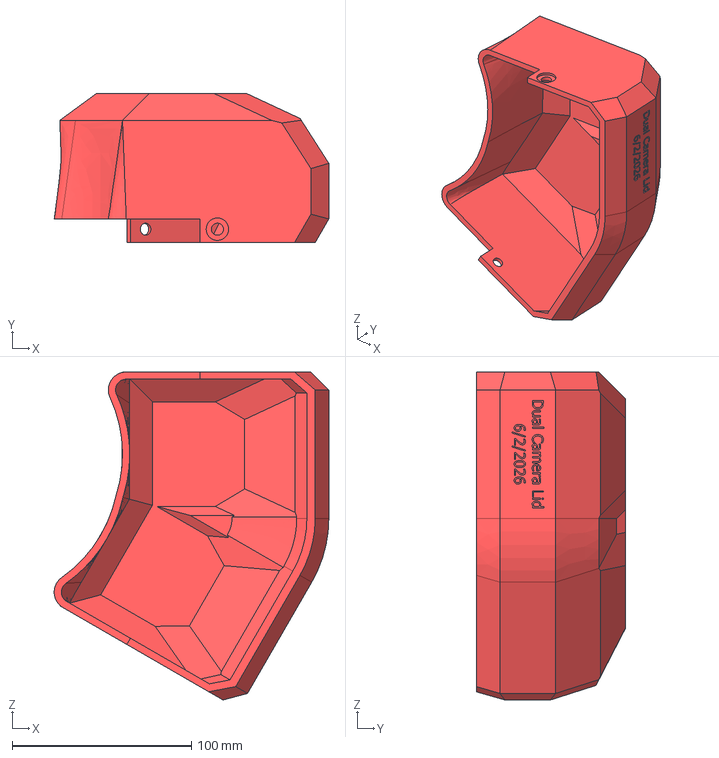
[picture p53: CAD file, 2026-06-02]
system_development/Damascus/V0.5.1/hardware development/Step Files/Dual Camera Lid.stp
153.1 x 83.2 x 182.8 mm
