ARTS-Laboratory/LPBF-Observer/system_development/Pittsburgh/v0.2/hardware_development/STEP Files/C .Replace - 10.stp

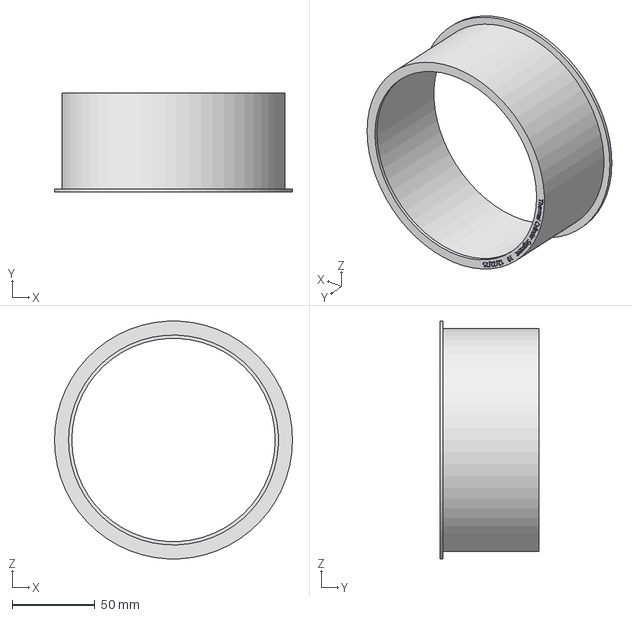
[picture p54: CAD file, 2026-04-30]
system_development/Pittsburgh/v0.2/hardware_development/STEP Files/C .Replace - 10.stp
144.0 x 60.0 x 143.8 mm
