ARTS-Laboratory/LPBF-Observer/system_development/Pittsburgh/v0.2/hardware_development/STEP Files/C .Replace - Face.stp

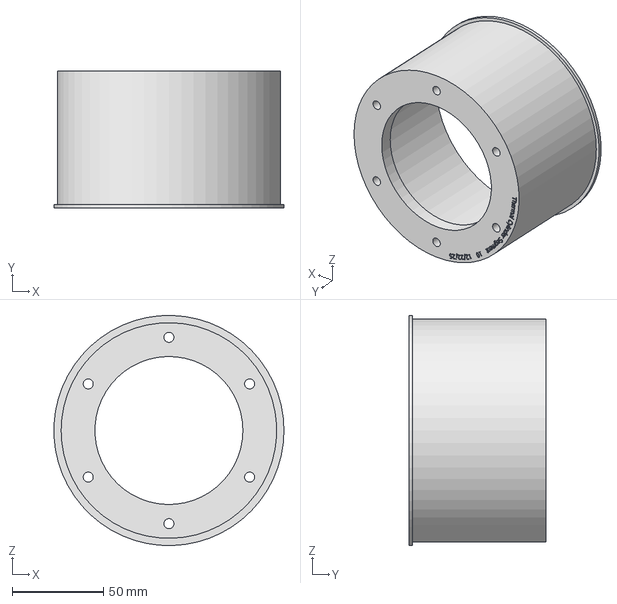
[picture p55: CAD file, 2026-04-30]
system_development/Pittsburgh/v0.2/hardware_development/STEP Files/C .Replace - Face.stp
125.9 x 75.0 x 126.0 mm
