ARTS-Laboratory/LPBF-Observer/system_development/Pittsburgh/v0.2/hardware_development/STEP Files/Spiral.stl

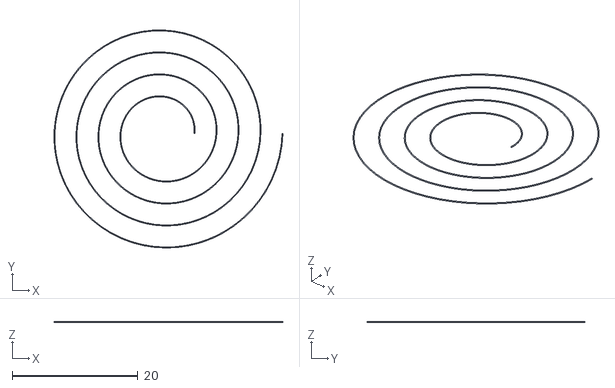
[picture p56: CAD file, 2026-04-30]
system_development/Pittsburgh/v0.2/hardware_development/STEP Files/Spiral.stl
36.4 x 34.6 x 0.148
