ARTS-Laboratory/LPBF-Observer/system_development/Pittsburgh/v0.2/hardware_development/STEP Files/Thermal Camera v0.2 LID.stp

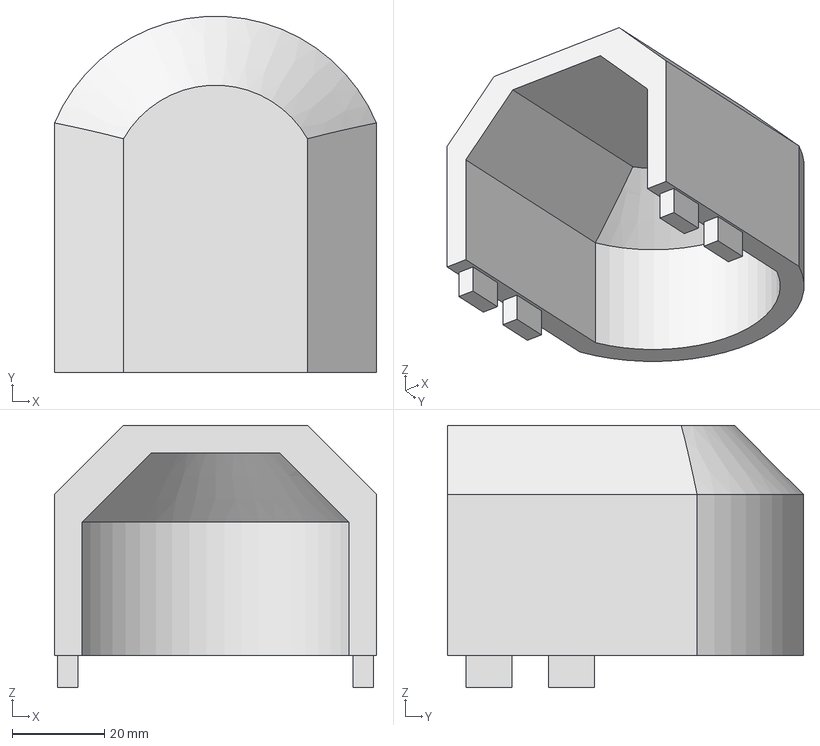
[picture p57: CAD file, 2026-04-30]
system_development/Pittsburgh/v0.2/hardware_development/STEP Files/Thermal Camera v0.2 LID.stp
70.0 x 77.4 x 57.0 mm
