ARTS-Laboratory/LPBF-Observer/system_development/Pittsburgh/v0.2/hardware_development/STEP Files/New Thermal Lid.stp

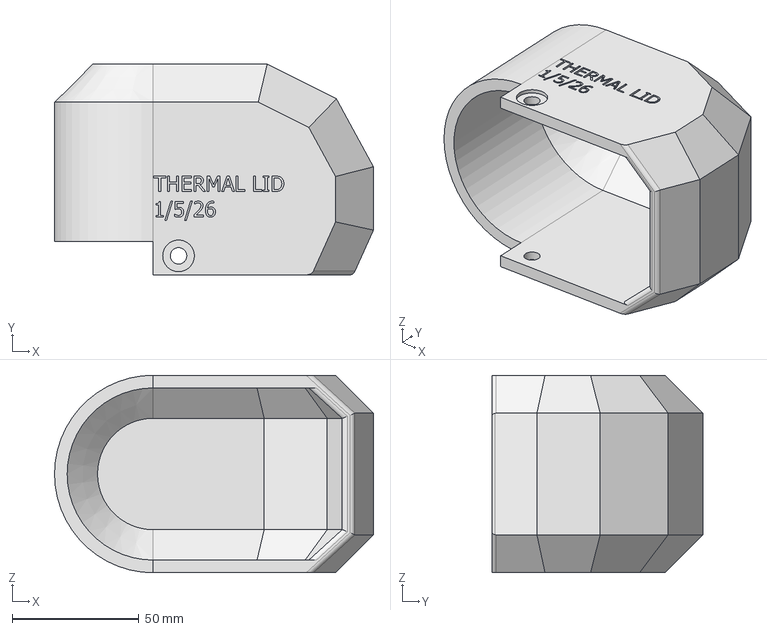
[picture p58: CAD file, 2026-04-30]
system_development/Pittsburgh/v0.2/hardware_development/STEP Files/New Thermal Lid.stp
126.0 x 83.2 x 78.0 mm
