ARTS-Laboratory/LPBF-Observer/system_development/Damascus/V0.5.1/software development/event_optical/iteration_2/Frame Generator/reconstructions/event_recording_0_015627_PM_10022026/count_log/frame_0.130000s_8875.png

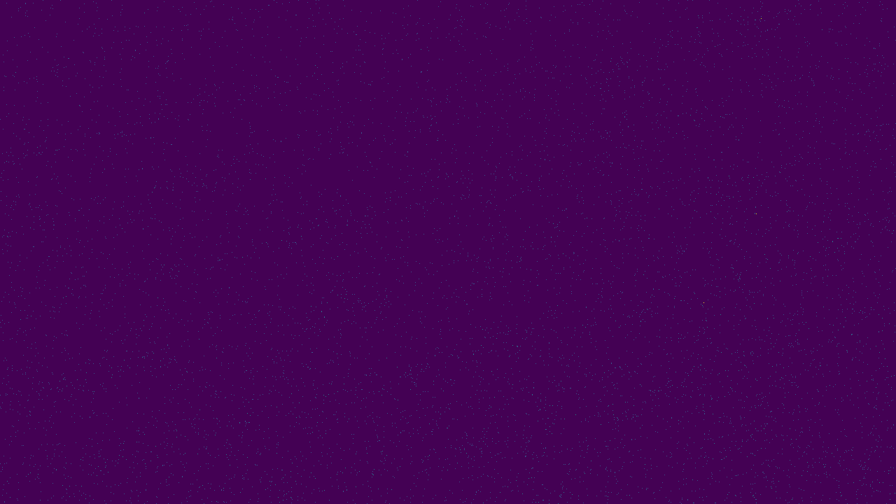
system_development/Damascus/V0.5.1/software development/event_optical/iteration_2/Frame Generator/reconstructions/event_recording_0_015627_PM_10022026/count_log/frame_0.130000s_8875.png
