ARTS-Laboratory/LPBF-Observer/system_development/Damascus/V0.5.1/software development/event_optical/iteration_2/Frame Generator/reconstructions/event_recording_13_124514_PM_09042026/count_log/frame_0.590000s_3153.png

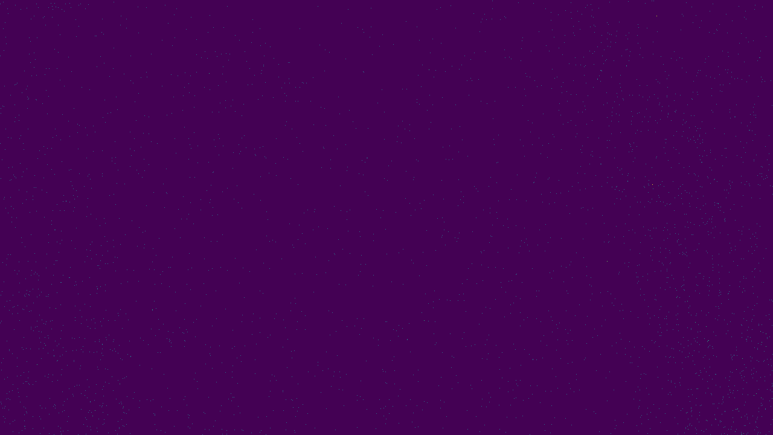
system_development/Damascus/V0.5.1/software development/event_optical/iteration_2/Frame Generator/reconstructions/event_recording_13_124514_PM_09042026/count_log/frame_0.590000s_3153.png
