ARTS-Laboratory/LPBF-Observer/system_development/Damascus/V0.5.1/media/Welding_Test_08142026/README.md

This folder contains pictures from welding test conducted on 14th Aug 2026.
