ARTS-Laboratory/LPBF-Observer/system_development/Pittsburgh/v0.2/software_development/Calibration Files/Xi 400 SN25114061/Kennlinie_combined.csv

Raw_M20_100 | Temp_M20_100 | Raw_0_250 | Temp_0_250 | Raw_150_900 | Temp_150_900
-3317 | -45.06592923 | -705 | -25.10195522 | -105 | -26.23266435
-3316 | -45.02142852 | -704 | -24.96611221 | -104 | -25.18994362
-3315 | -44.97692781 | -703 | -24.83037986 | -103 | -24.1530225
-3314 | -44.9324271 | -702 | -24.69492732 | -102 | -23.13467565
-3313 | -44.88794741 | -701 | -24.55979308 | -101 | -22.13456514
-3312 | -44.8435242 | -700 | -24.42492789 | -100 | -21.15188338
-3311 | -44.79910255 | -699 | -24.29034591 | -99 | -20.18586236
-3310 | -44.75475662 | -698 | -24.15606966 | -98 | -19.23583326
-3309 | -44.71041068 | -697 | -24.02205869 | -97 | -18.30109022
-3308 | -44.66612372 | -696 | -23.88833031 | -96 | -17.38107697
-3307 | -44.62185485 | -695 | -23.75489928 | -95 | -16.47517581
-3306 | -44.57762488 | -694 | -23.62172984 | -94 | -15.58284731
-3305 | -44.53343286 | -693 | -23.48883844 | -93 | -14.70358265
-3304 | -44.48925948 | -692 | -23.35624009 | -92 | -13.83693162
-3303 | -44.44514409 | -691 | -23.2238997 | -91 | -12.98239221
-3302 | -44.40102869 | -690 | -23.09182901 | -90 | -12.13957469
-3301 | -44.35698792 | -689 | -22.96005102 | -89 | -11.30803873
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
