ARTS-Laboratory/LPBF-Observer/system_development/Damascus/V0.5.1/media/Welding_Test_08142026/20260814_141421.jpg

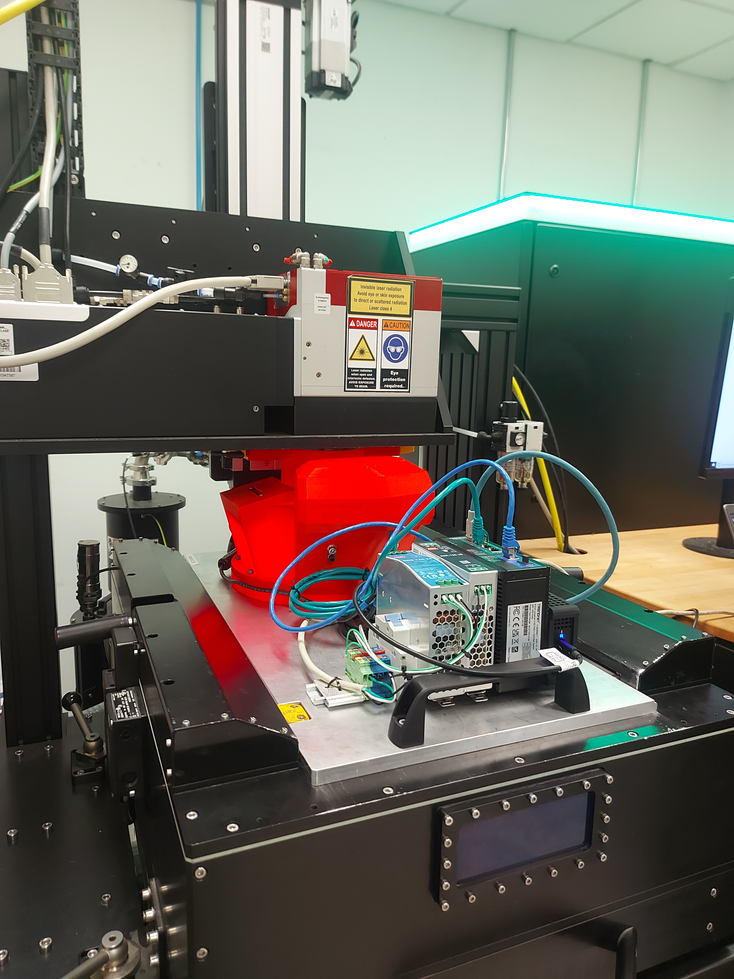
system_development/Damascus/V0.5.1/media/Welding_Test_08142026/20260814_141421.jpg
